Megazoids-Hut/Mini-ESP32-TV/images/1.JPG

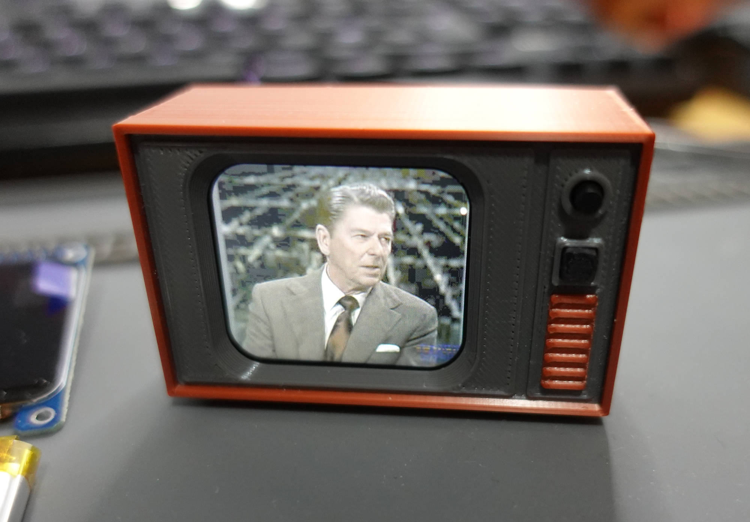
images/1.JPG
