Megazoids-Hut/Mini-ESP32-TV/images/2.JPG

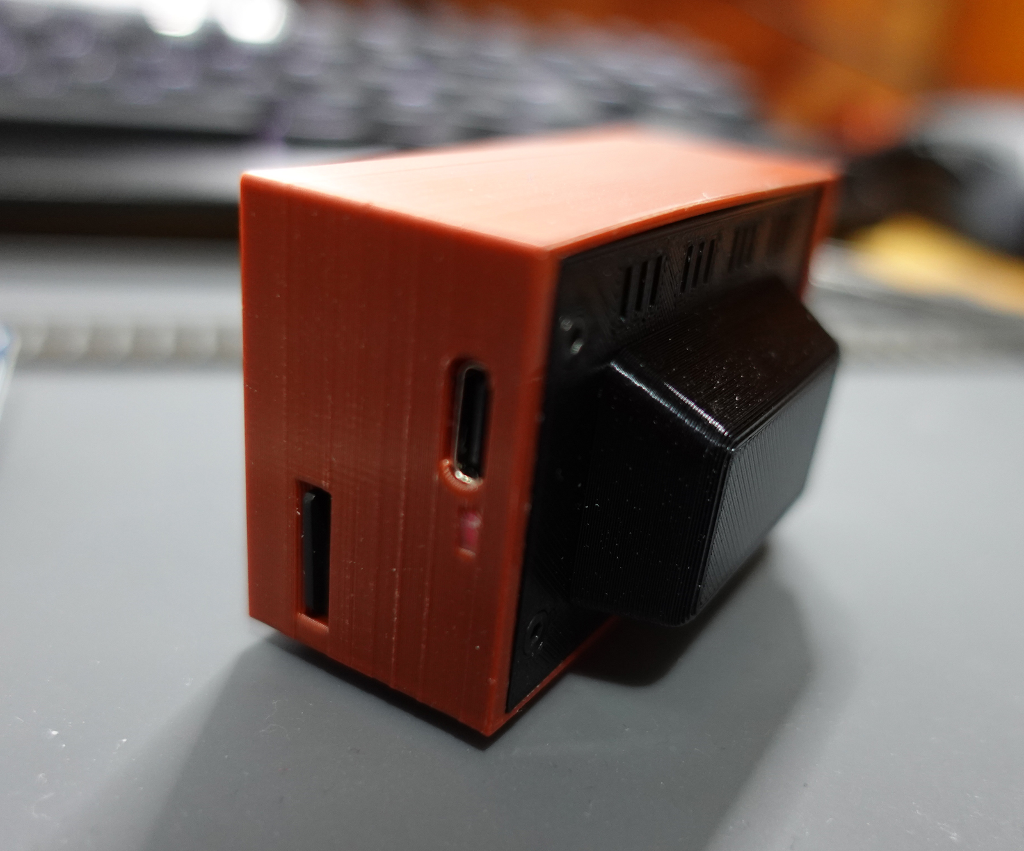
images/2.JPG
