Megazoids-Hut/Mini-ESP32-TV/images/3.JPG

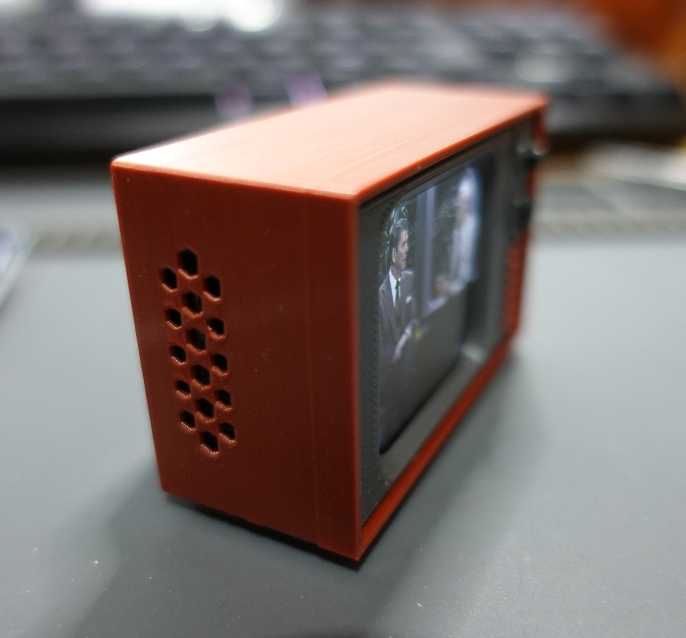
images/3.JPG
