Megazoids-Hut/Mini-ESP32-TV/images/4.JPG

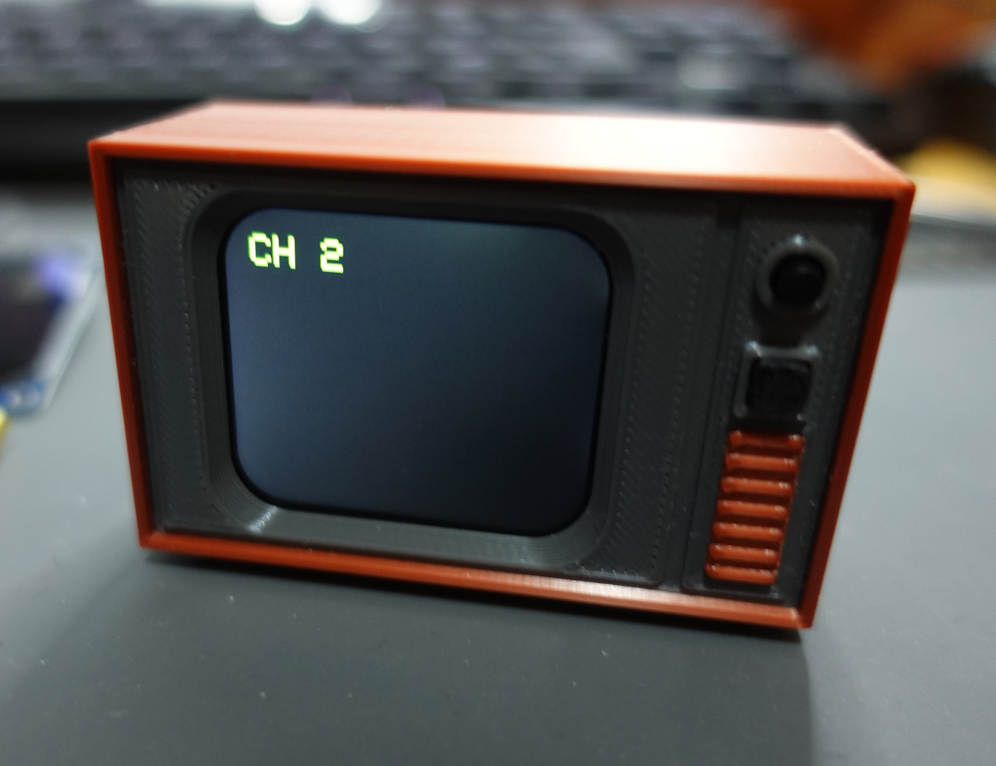
images/4.JPG
