Megazoids-Hut/Mini-ESP32-TV/images/5.JPG

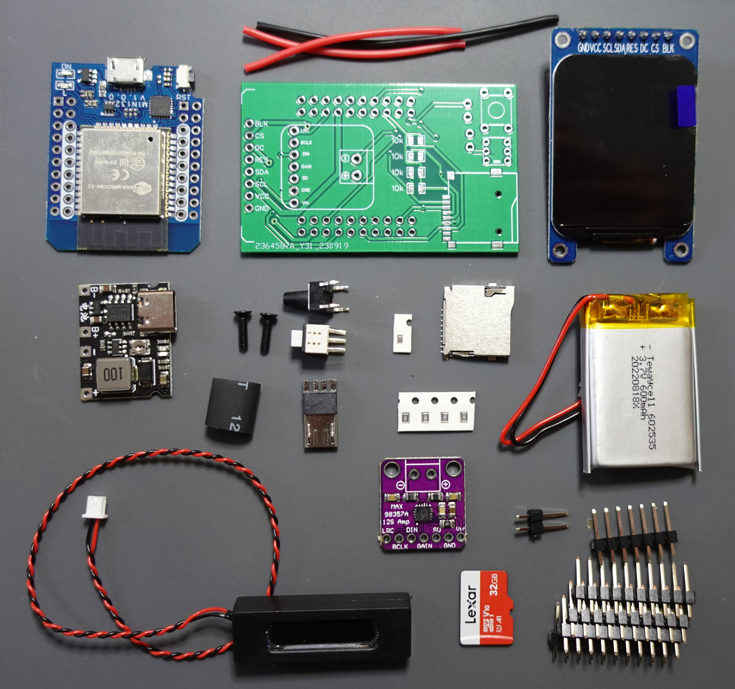
images/5.JPG
