Megazoids-Hut/Mini-ESP32-TV/images/7.JPG

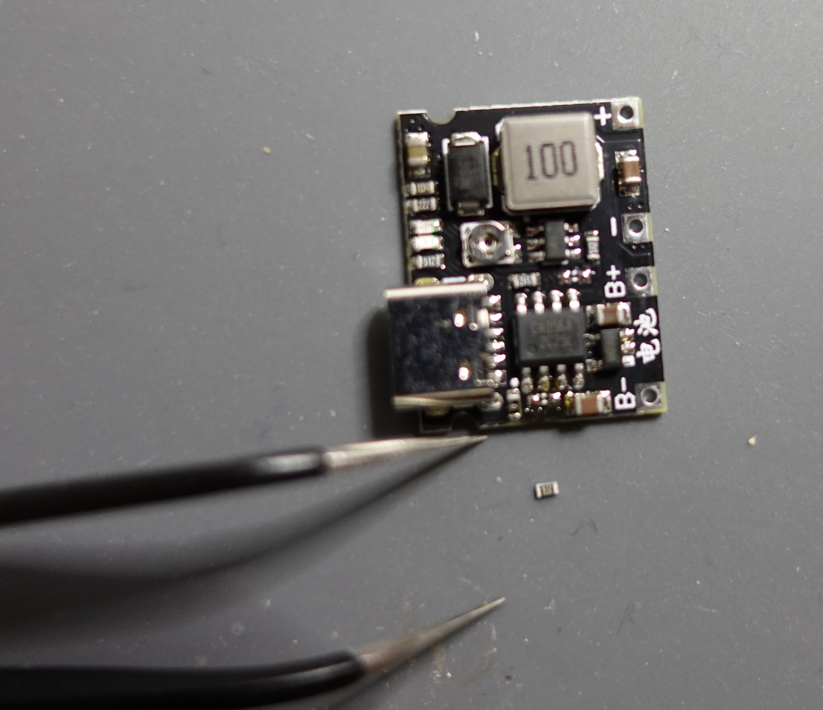
images/7.JPG
