Megazoids-Hut/Mini-ESP32-TV/images/8.JPG

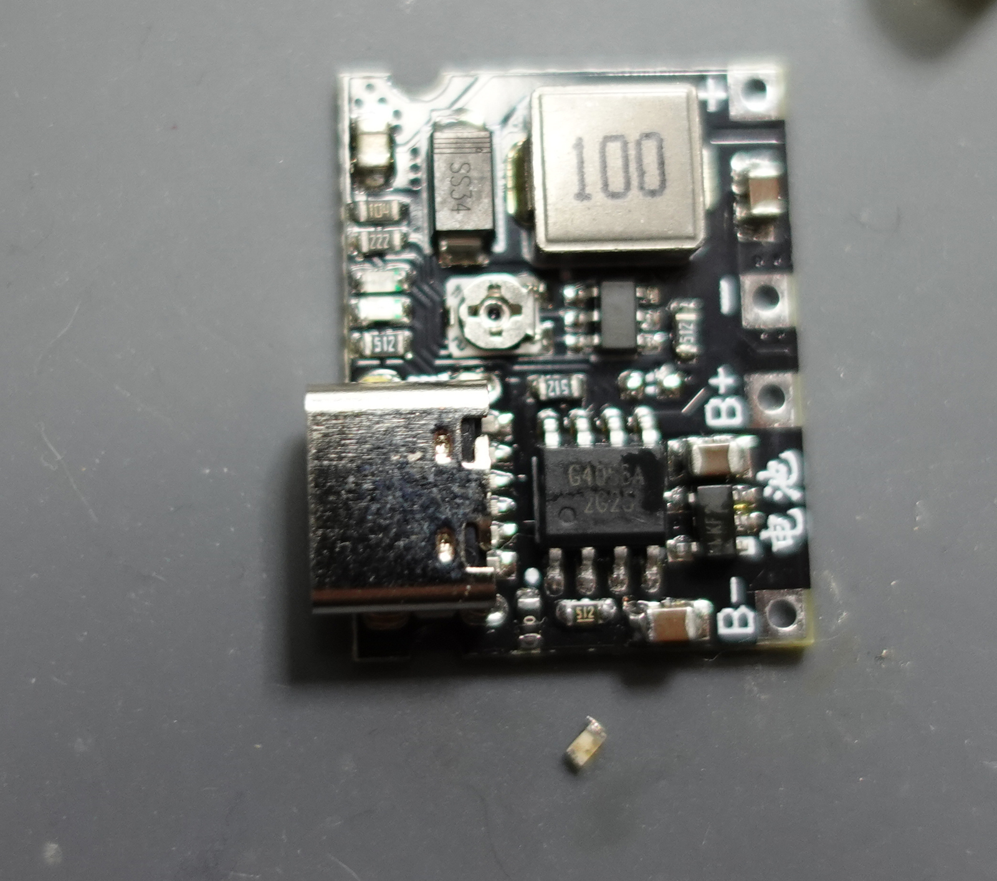
images/8.JPG
