Megazoids-Hut/Mini-ESP32-TV/images/9.JPG

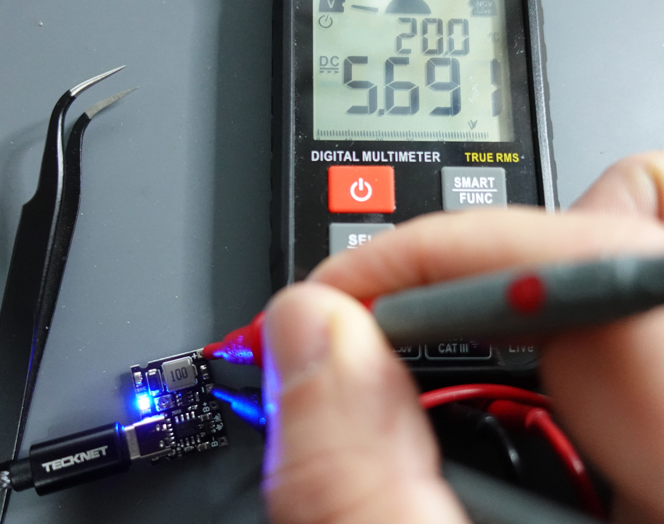
images/9.JPG
