Megazoids-Hut/Mini-ESP32-TV/images/10.JPG

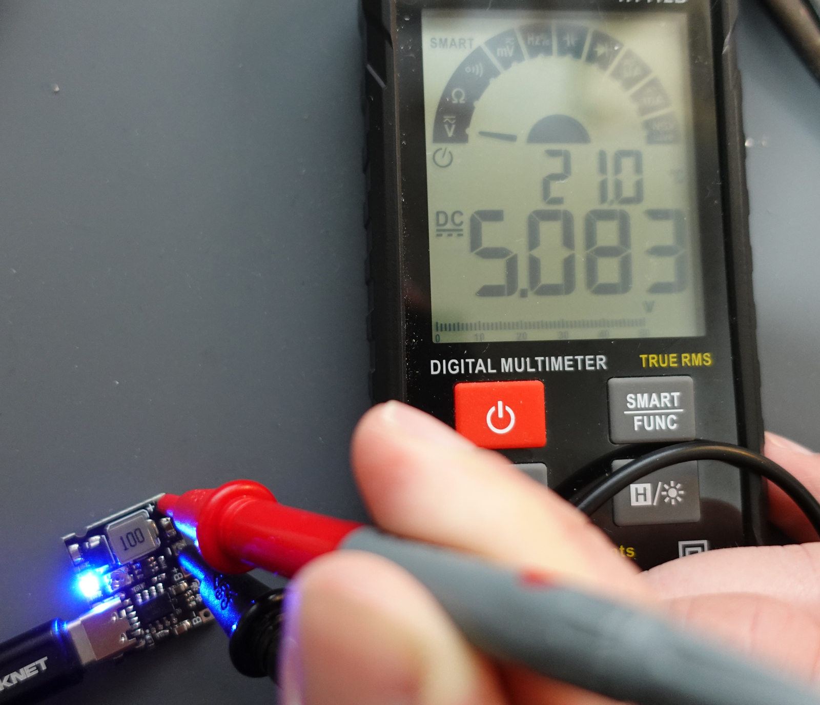
images/10.JPG
