Megazoids-Hut/Mini-ESP32-TV/images/11.jpg

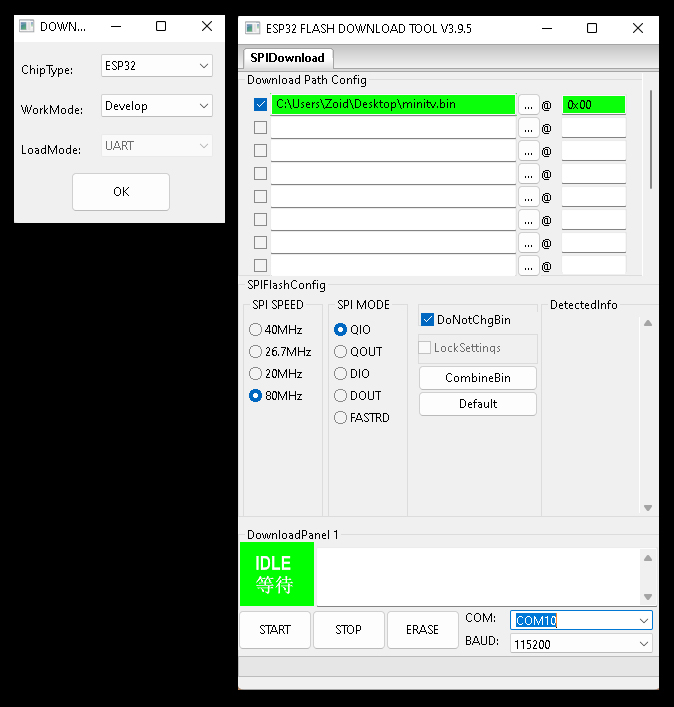
images/11.jpg
