Megazoids-Hut/Mini-ESP32-TV/images/12.jpg

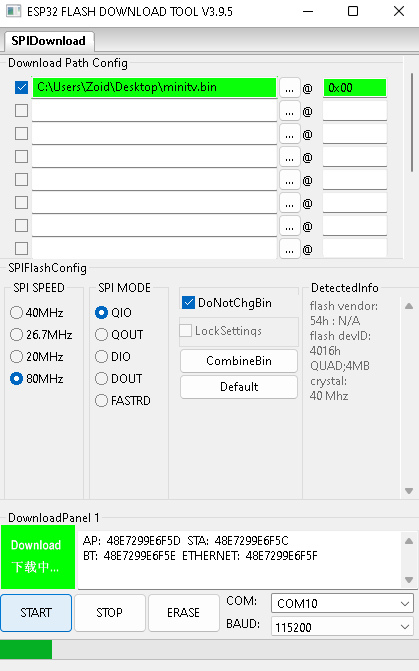
images/12.jpg
