Megazoids-Hut/Mini-ESP32-TV/images/13.JPG

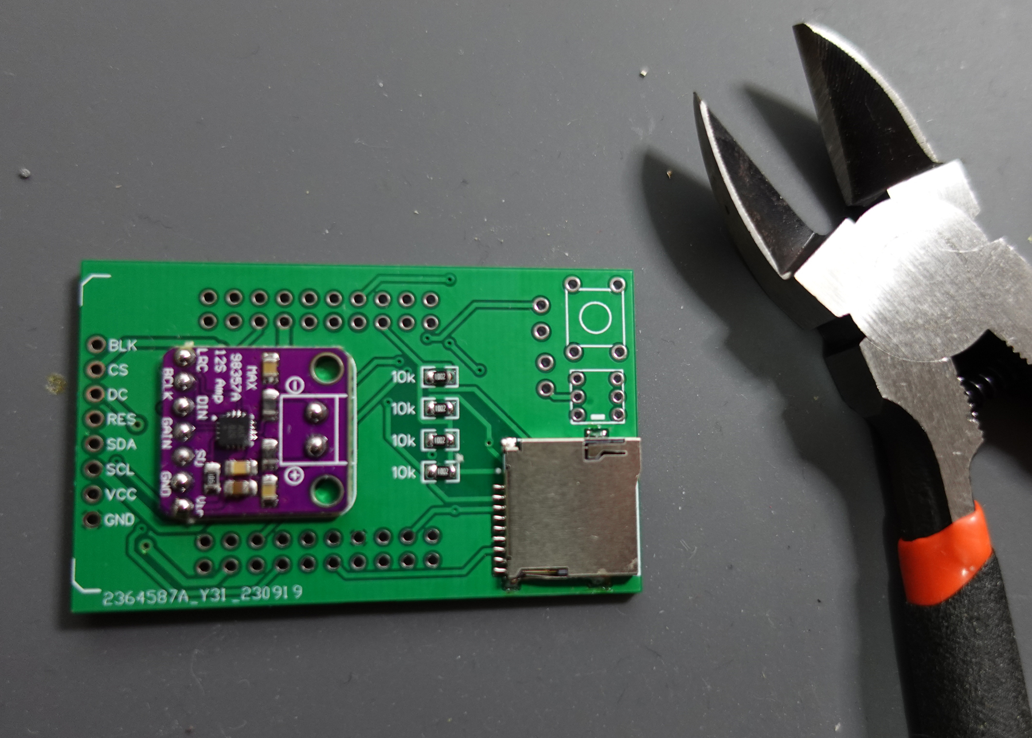
images/13.JPG
