Megazoids-Hut/Mini-ESP32-TV/images/14.JPG

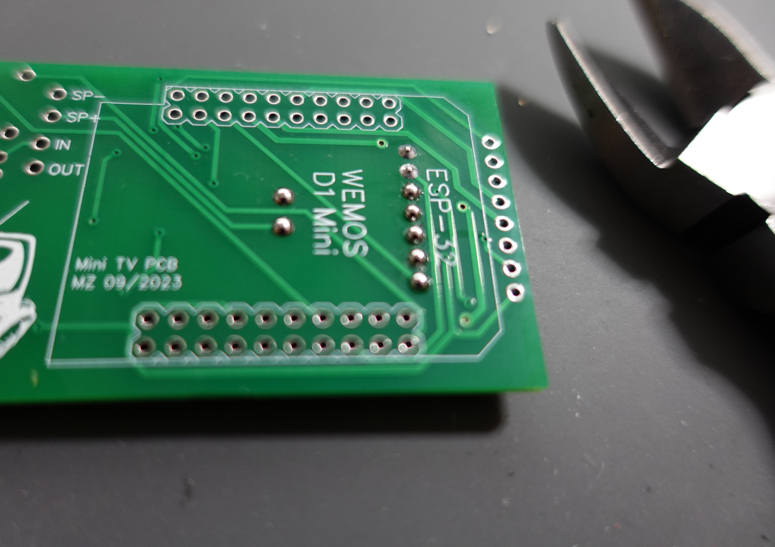
images/14.JPG
