Megazoids-Hut/Mini-ESP32-TV/images/15.JPG

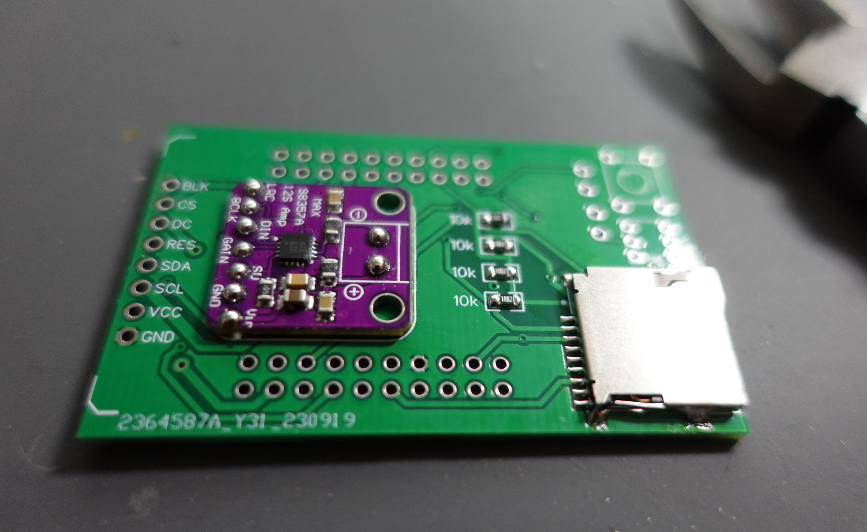
images/15.JPG
