Megazoids-Hut/Mini-ESP32-TV/images/16.jpg

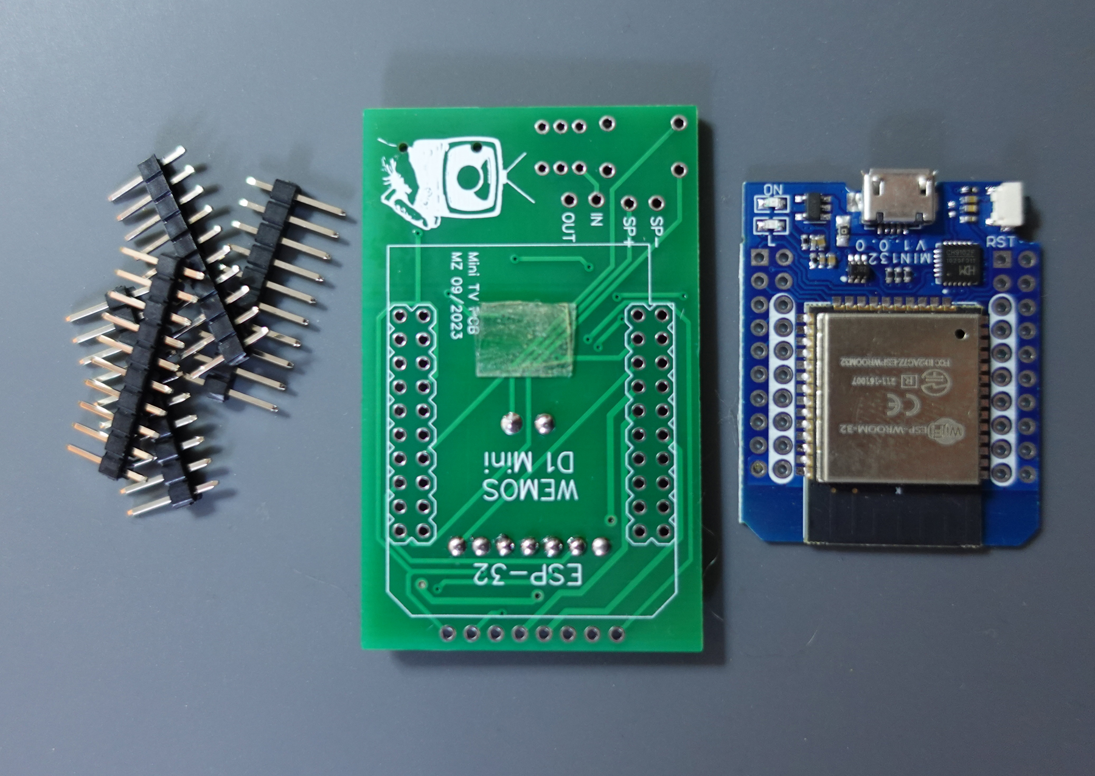
images/16.jpg
