Megazoids-Hut/Mini-ESP32-TV/images/17.jpg

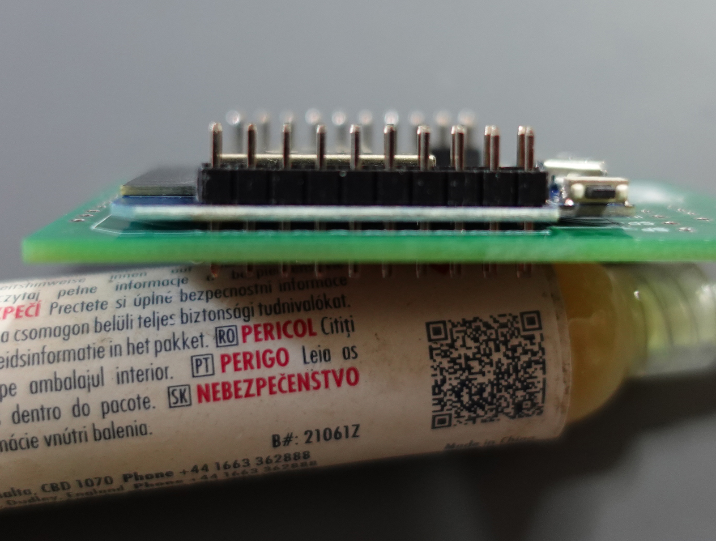
images/17.jpg
