Megazoids-Hut/Mini-ESP32-TV/images/18.jpg

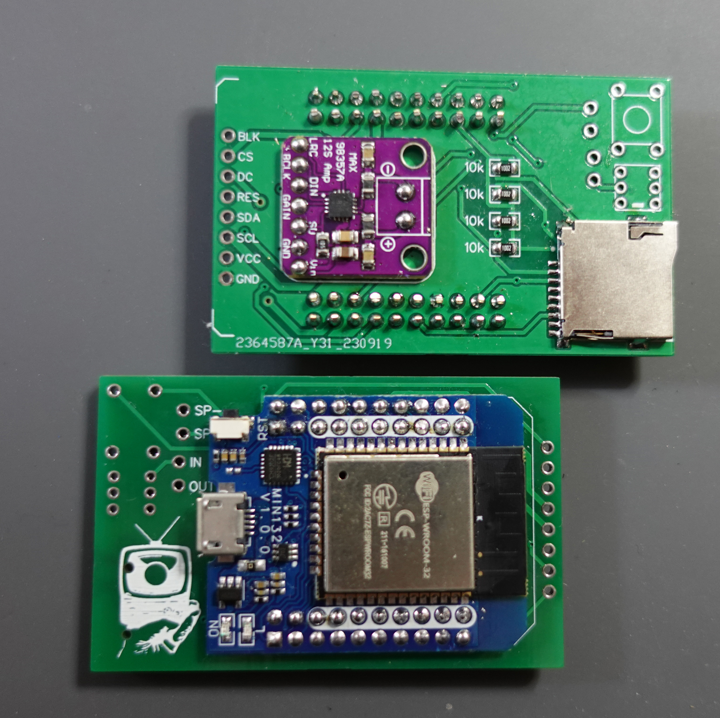
images/18.jpg
