Megazoids-Hut/Mini-ESP32-TV/images/19.jpg

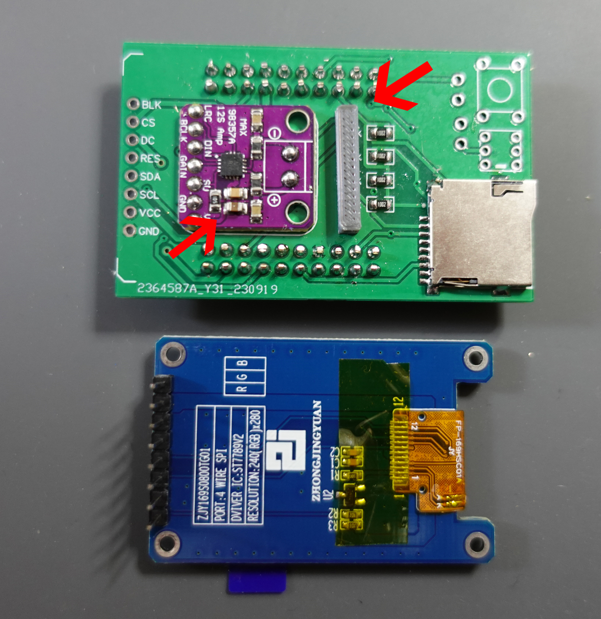
images/19.jpg
