Megazoids-Hut/Mini-ESP32-TV/images/20.jpg

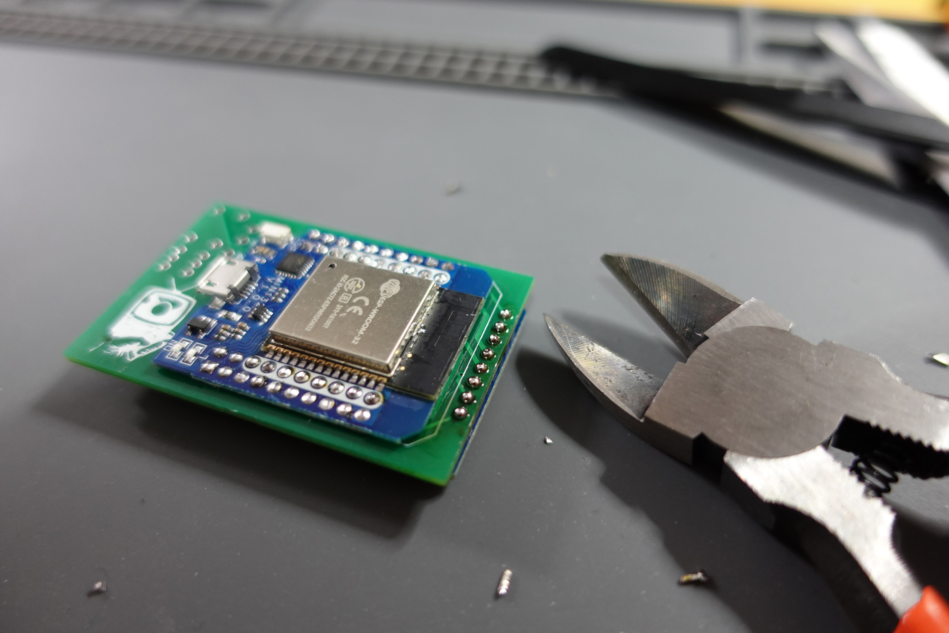
images/20.jpg
