Megazoids-Hut/Mini-ESP32-TV/images/21.jpg

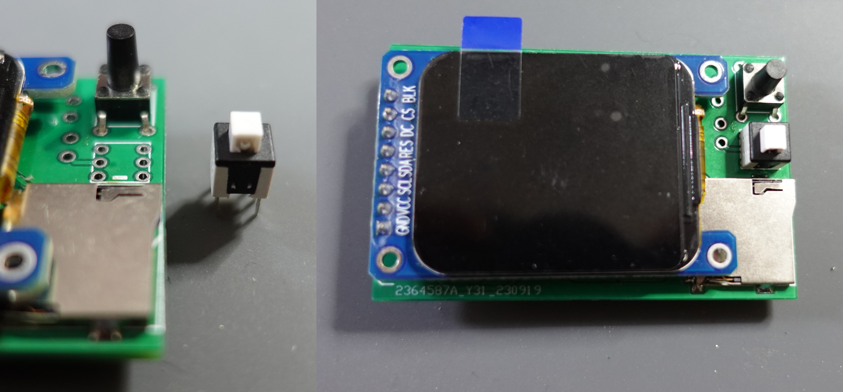
images/21.jpg
