Megazoids-Hut/Mini-ESP32-TV/images/22.jpg

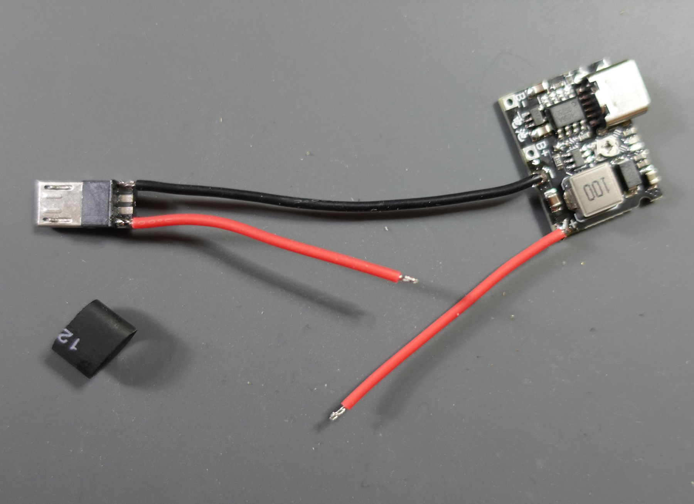
images/22.jpg
