Megazoids-Hut/Mini-ESP32-TV/images/23.jpg

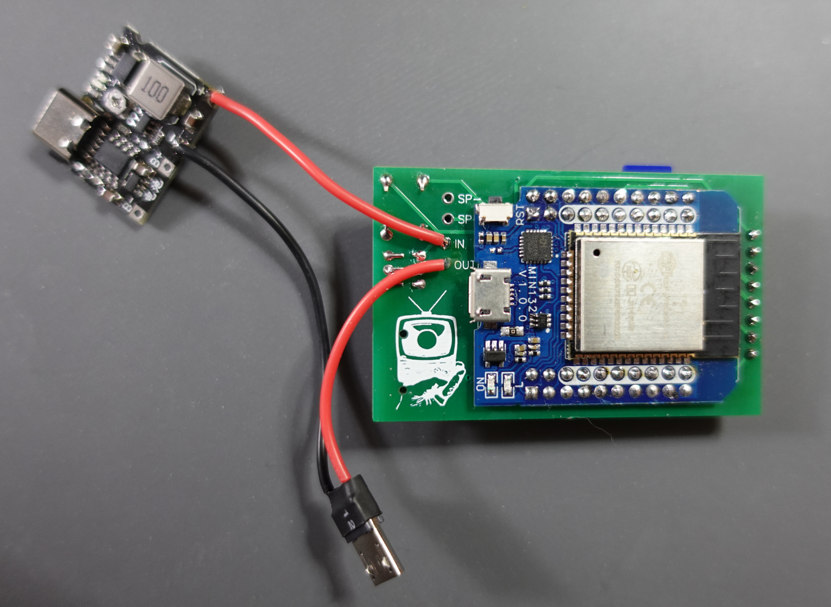
images/23.jpg
