Megazoids-Hut/Mini-ESP32-TV/images/24.jpg

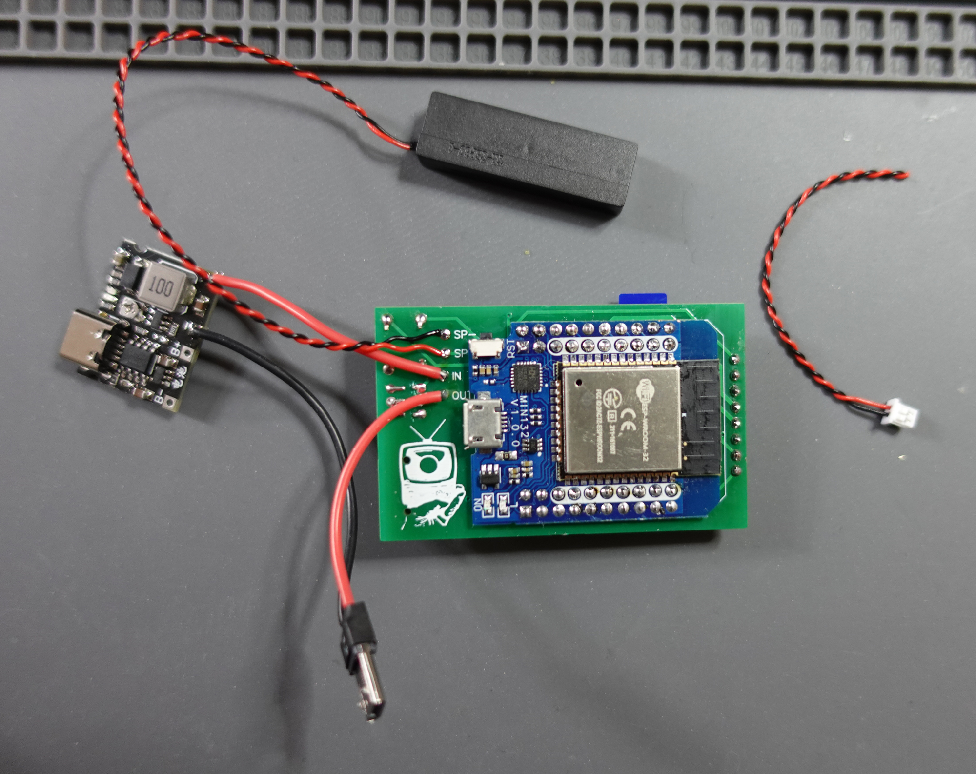
images/24.jpg
