Megazoids-Hut/Mini-ESP32-TV/images/25.JPG

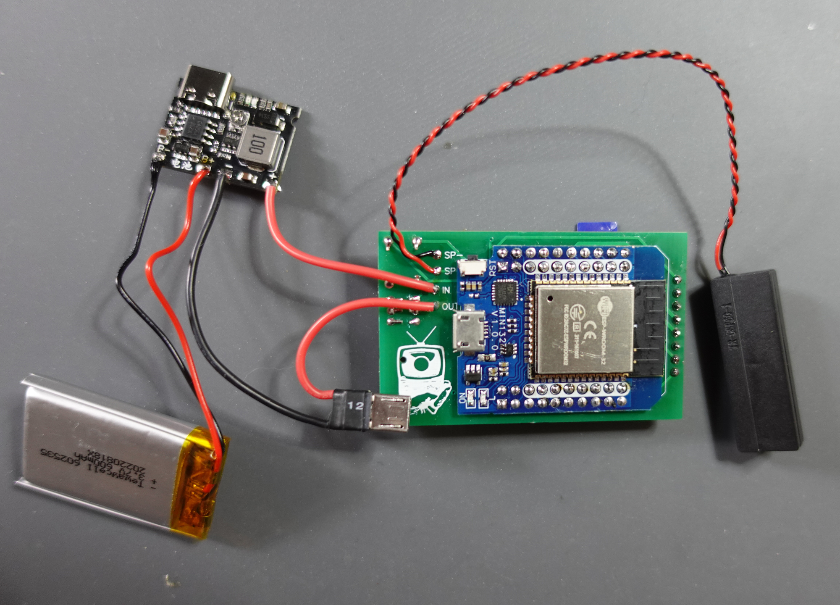
images/25.JPG
