Megazoids-Hut/Mini-ESP32-TV/images/26.jpg

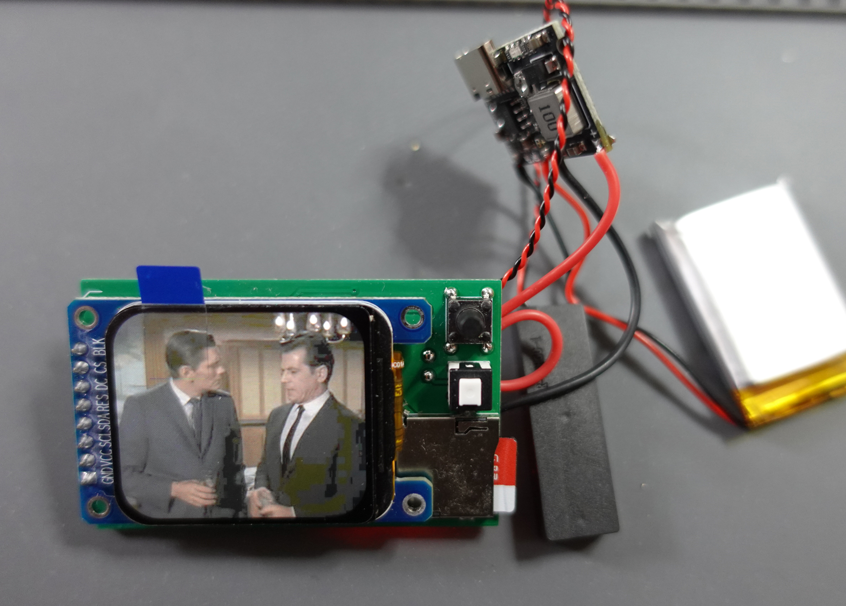
images/26.jpg
