Megazoids-Hut/Mini-ESP32-TV/images/27.jpg

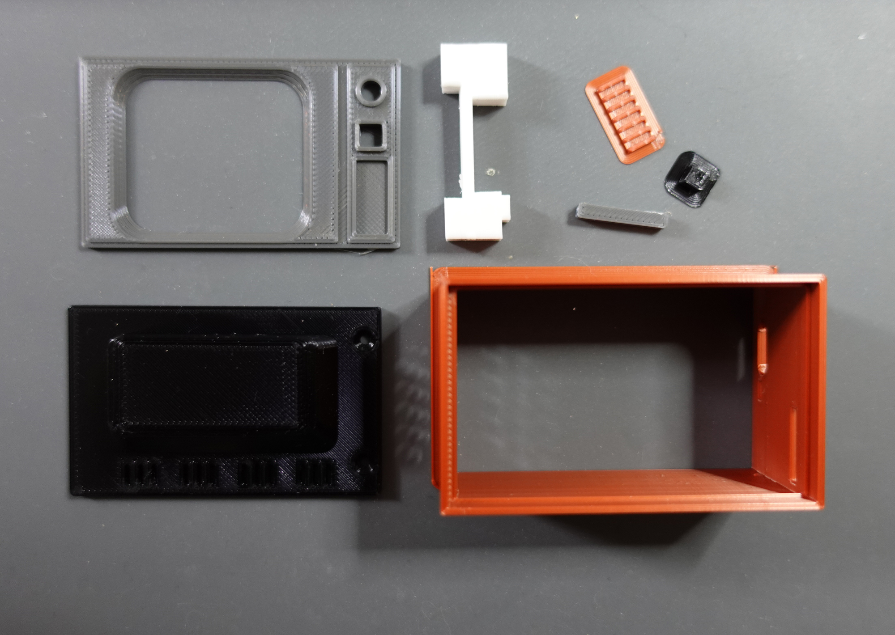
images/27.jpg
