Megazoids-Hut/Mini-ESP32-TV/images/28.jpg

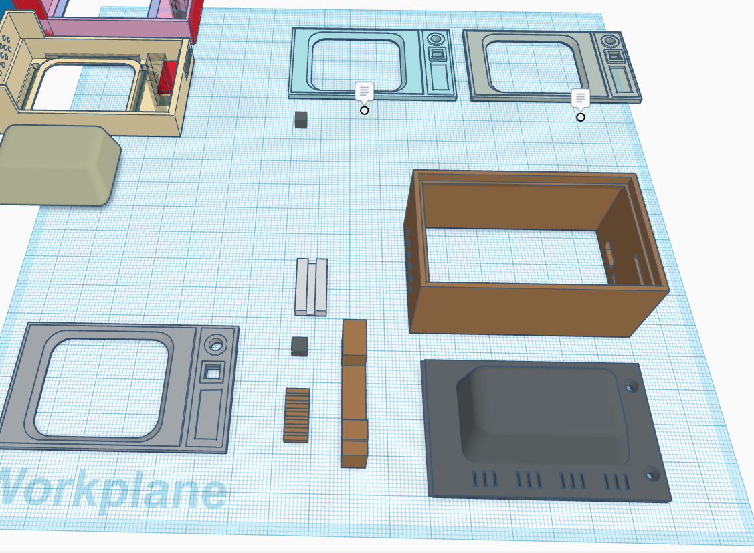
images/28.jpg
