Megazoids-Hut/Mini-ESP32-TV/images/29.jpg

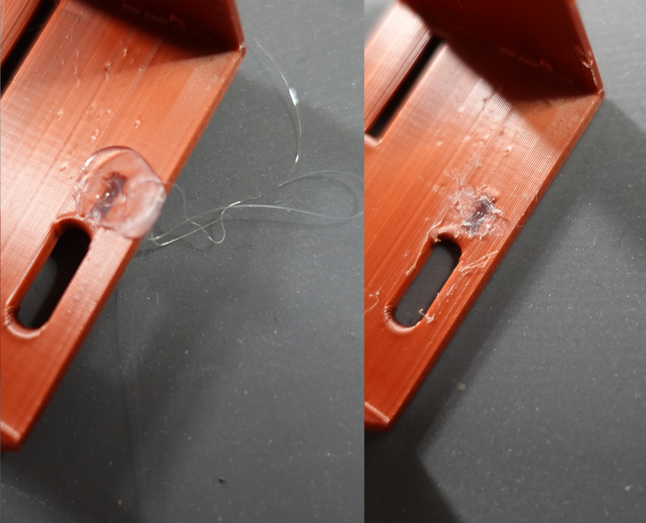
images/29.jpg
