Megazoids-Hut/Mini-ESP32-TV/images/30.jpg

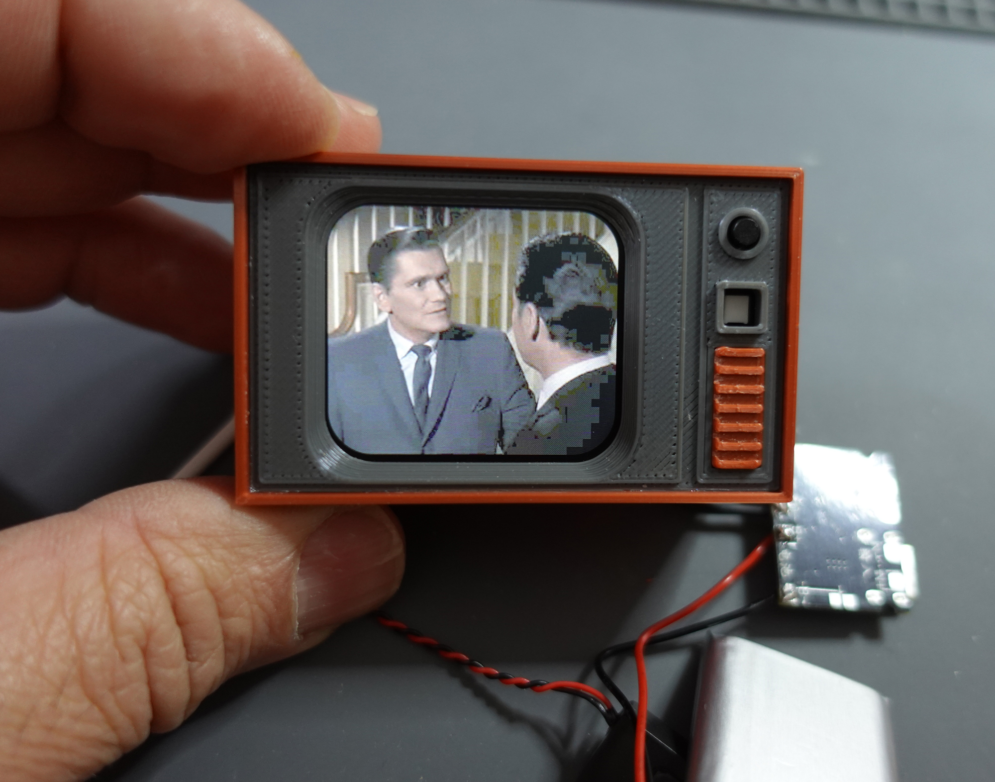
images/30.jpg
