Megazoids-Hut/Mini-ESP32-TV/images/31.jpg

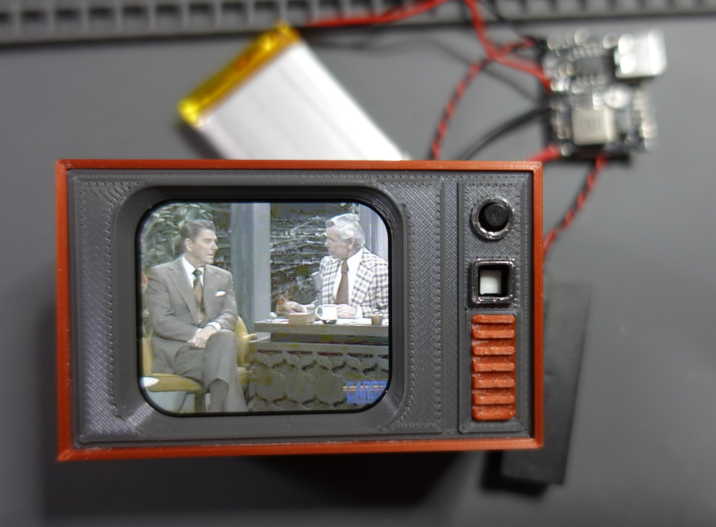
images/31.jpg
