Megazoids-Hut/Mini-ESP32-TV/images/33.jpg

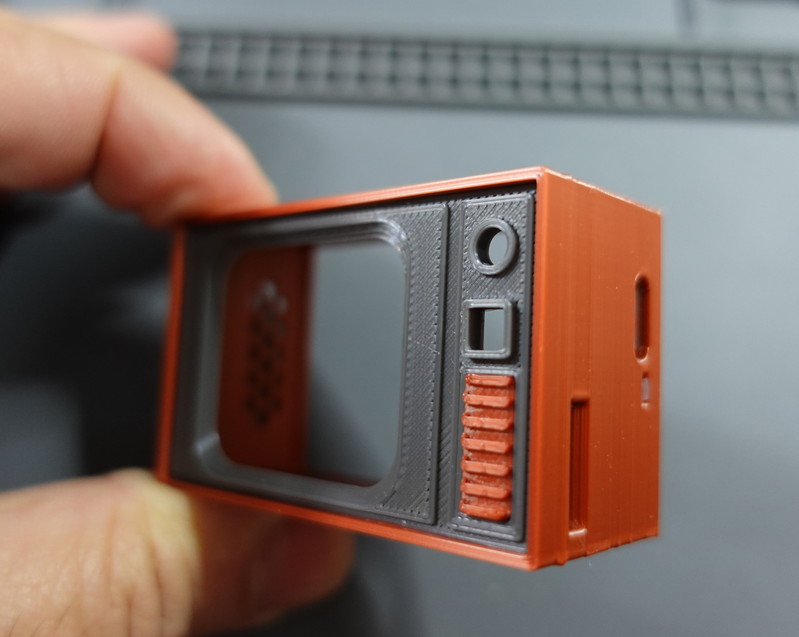
images/33.jpg
