Megazoids-Hut/Mini-ESP32-TV/images/34.jpg

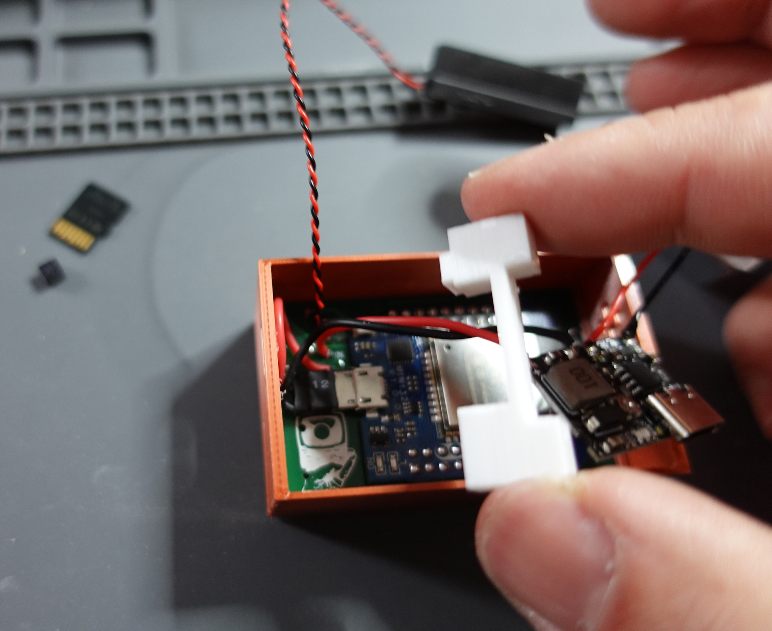
images/34.jpg
