Megazoids-Hut/Mini-ESP32-TV/images/35.jpg

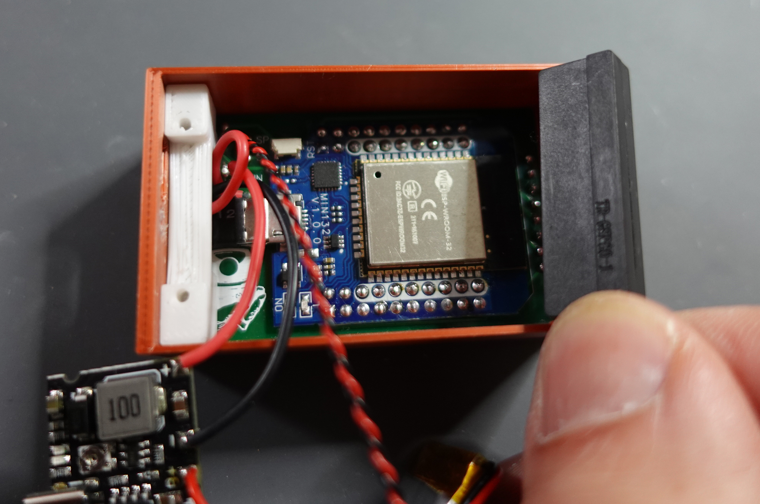
images/35.jpg
