Megazoids-Hut/Mini-ESP32-TV/images/36.jpg

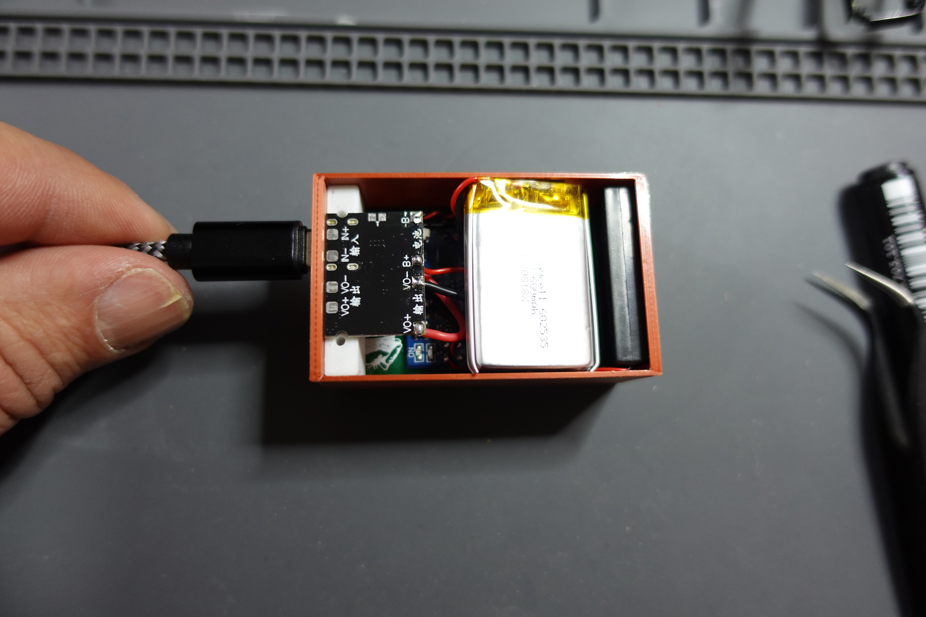
images/36.jpg
