Megazoids-Hut/Mini-ESP32-TV/images/37.jpg

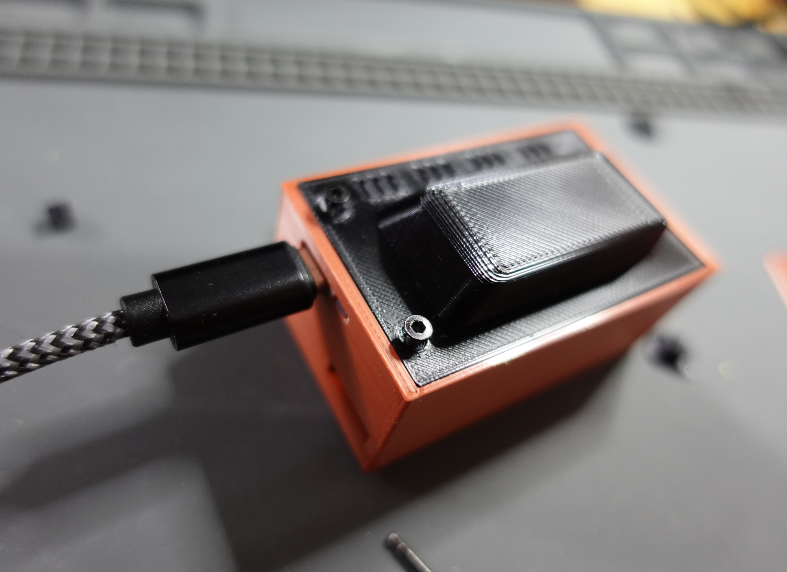
images/37.jpg
