Megazoids-Hut/Mini-ESP32-TV/images/38.jpg

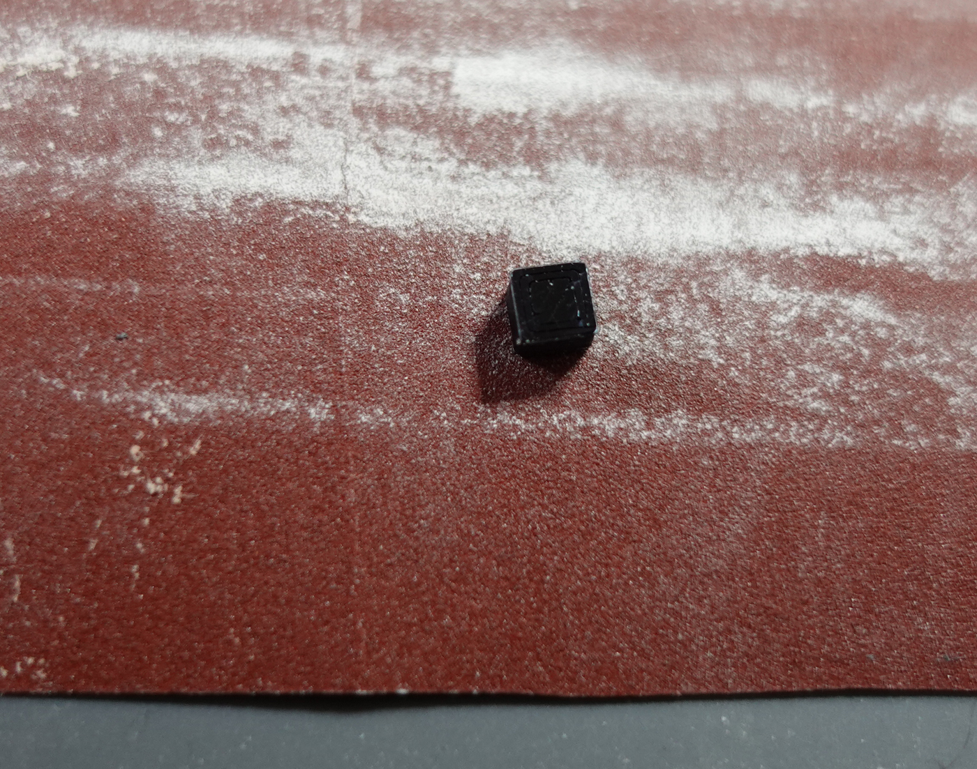
images/38.jpg
