Megazoids-Hut/Mini-ESP32-TV/images/39.jpg

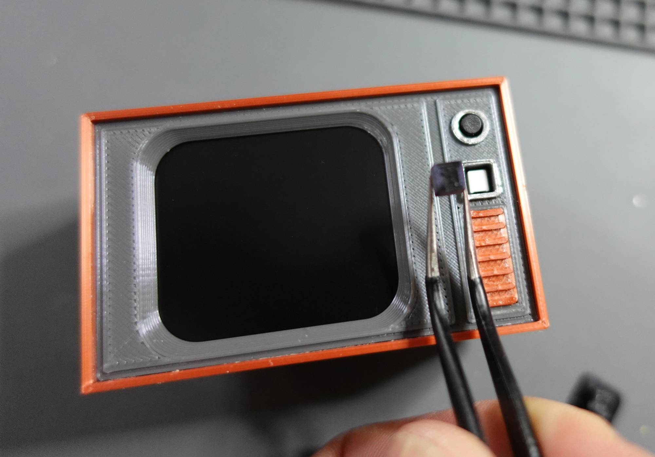
images/39.jpg
