Megazoids-Hut/Mini-ESP32-TV/images/40.jpg

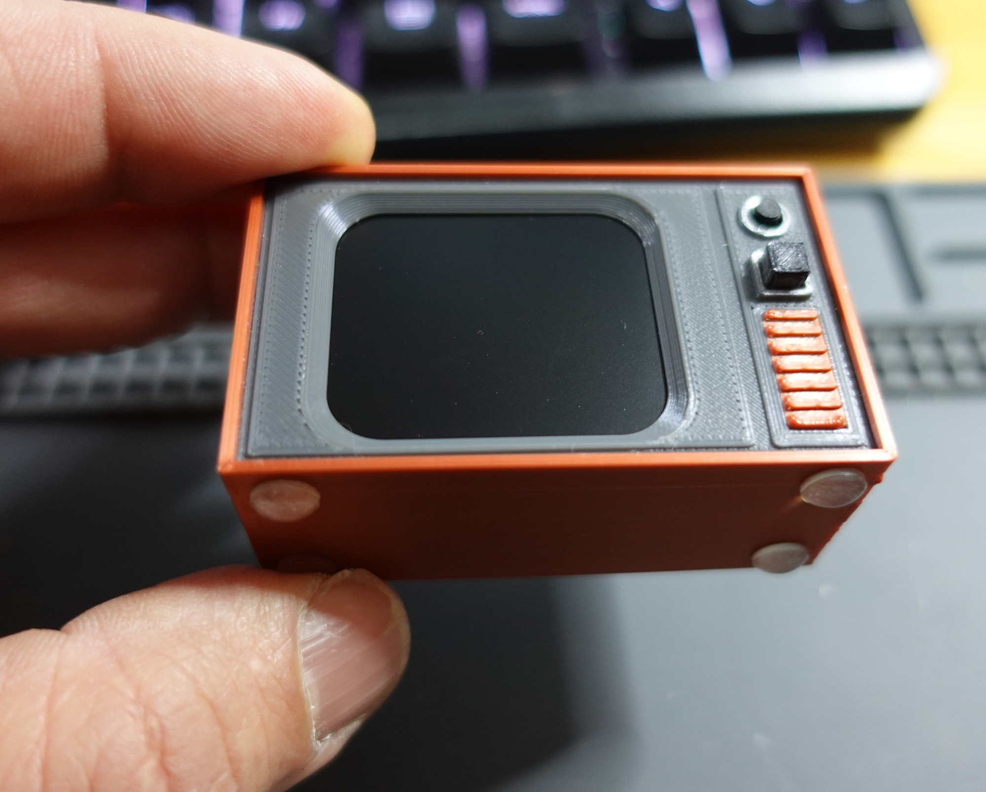
images/40.jpg
