Megazoids-Hut/Mini-ESP32-TV/images/41.jpg

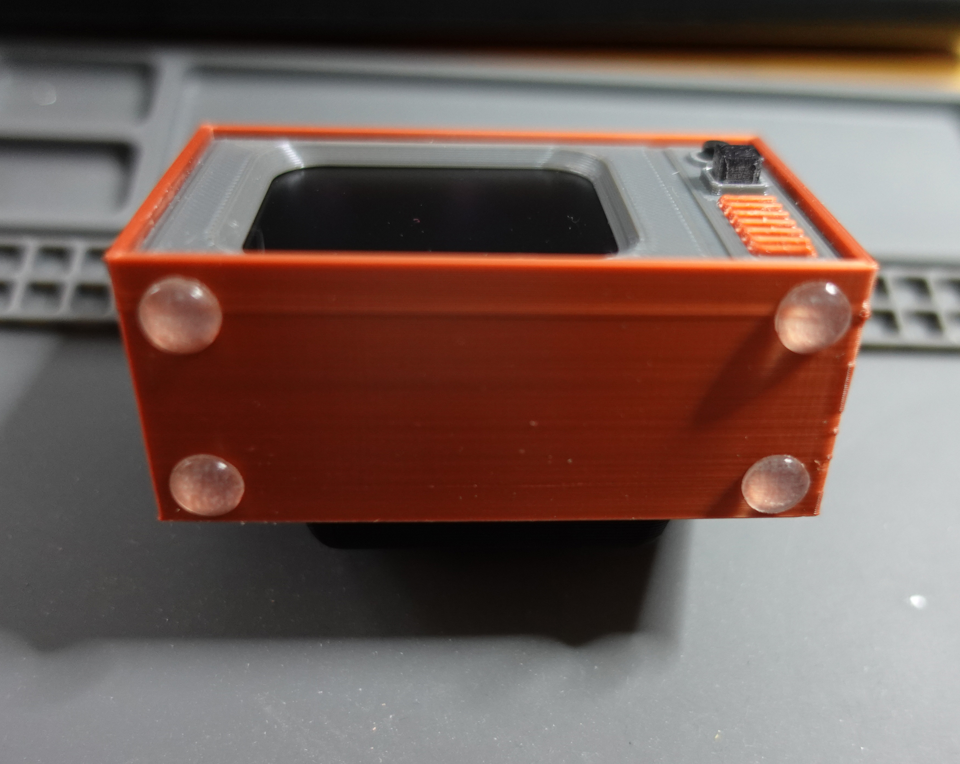
images/41.jpg
