Megazoids-Hut/Mini-ESP32-TV/images/42.jpg

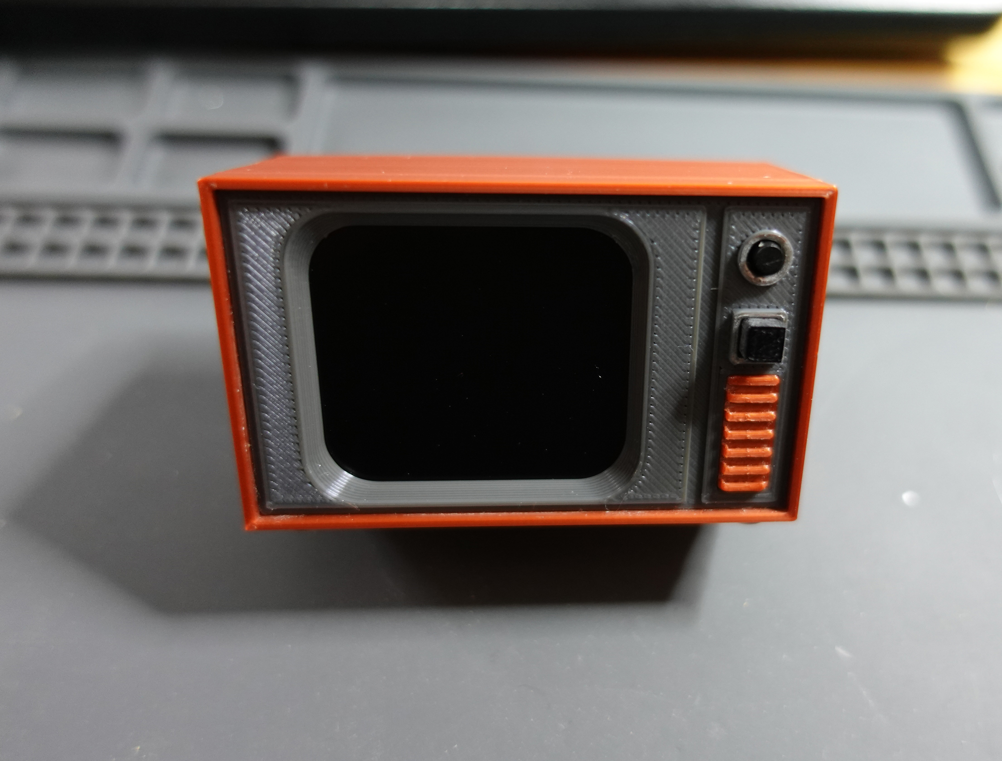
images/42.jpg
