Megazoids-Hut/Mini-ESP32-TV/images/43.jpg

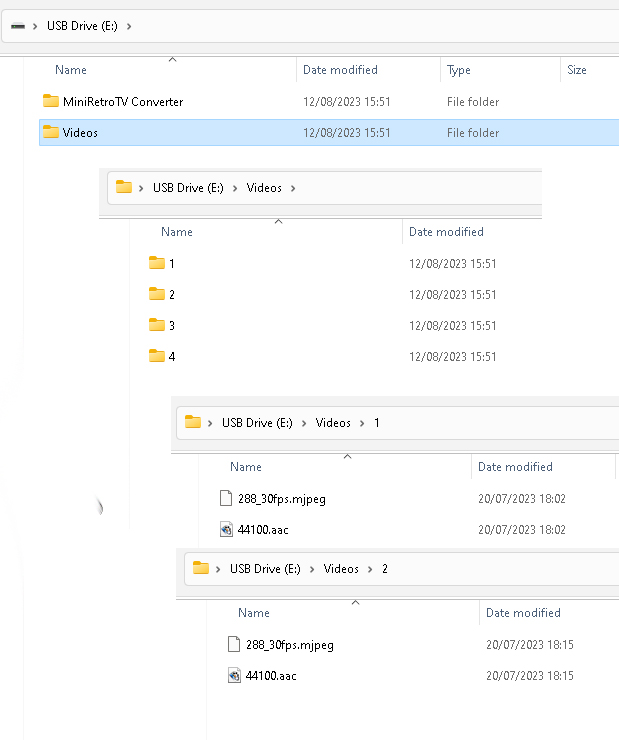
images/43.jpg
